bultza/IRIS2-hardware/IRIS2_PCB_CPU/docs/IRIS2_Batteries.png

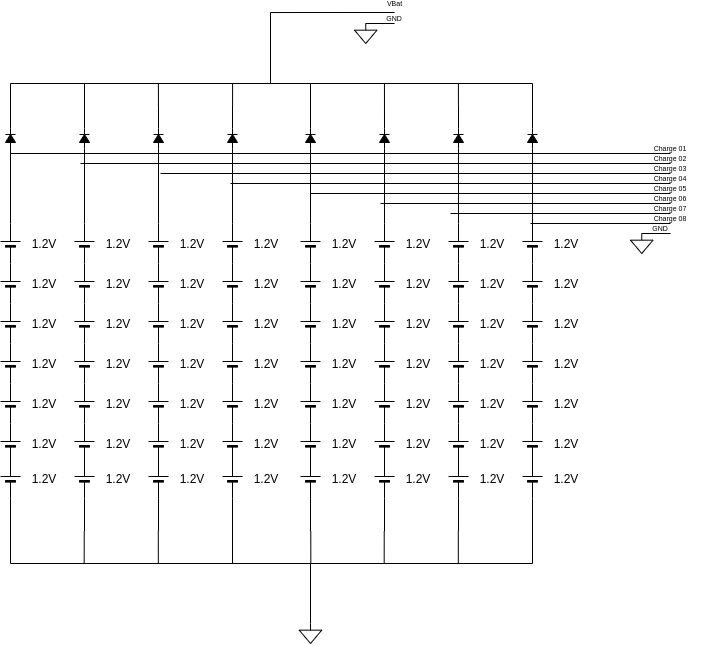
IRIS2_PCB_CPU/docs/IRIS2_Batteries.png
