bultza/IRIS2-hardware/IRIS2_PCB_CPU/Project Outputs for IRIS2_PCB_CPU/3D Render BOTTOM.png

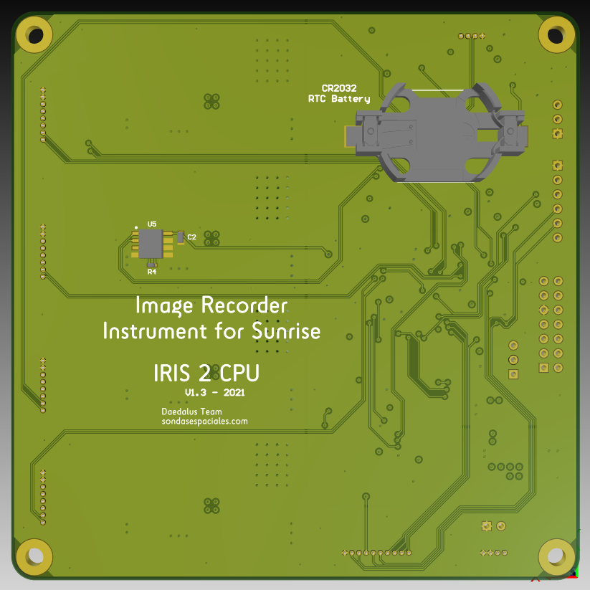
IRIS2_PCB_CPU/Project Outputs for IRIS2_PCB_CPU/3D Render BOTTOM.png
