bultza/IRIS2-hardware/IRIS2_PCB_CPU/Project Outputs for IRIS2_PCB_CPU/3D Render TOP.png

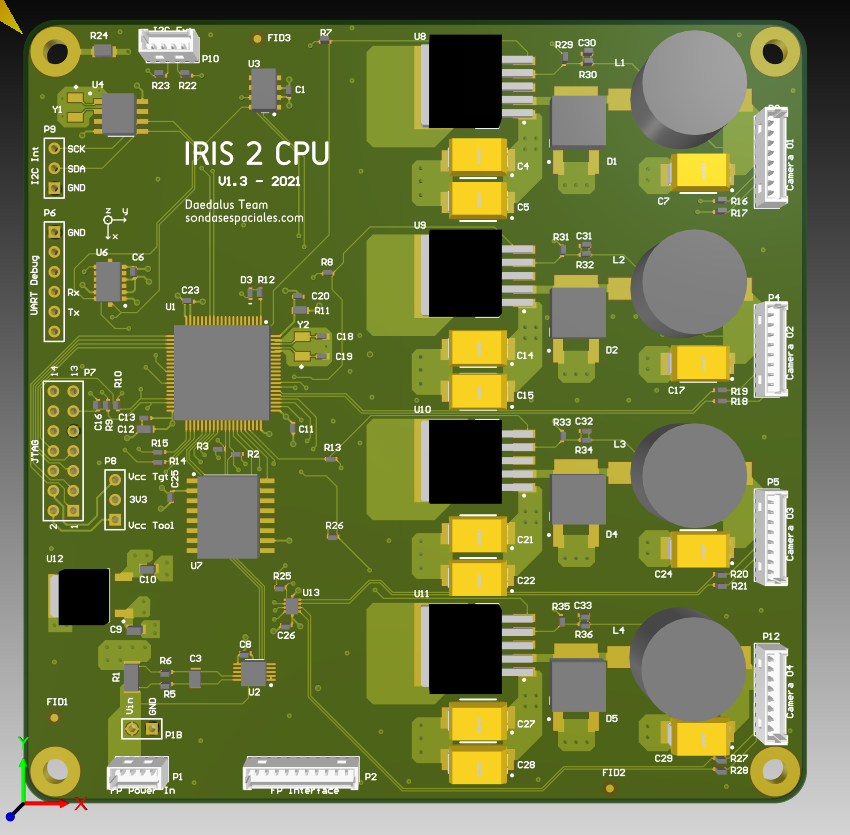
IRIS2_PCB_CPU/Project Outputs for IRIS2_PCB_CPU/3D Render TOP.png
