bultza/IRIS2-hardware/IRIS2_PCB_CPU/Project Outputs for IRIS2_PCB_CPU/20210401_IRIS2_CPU_LayerStack.png

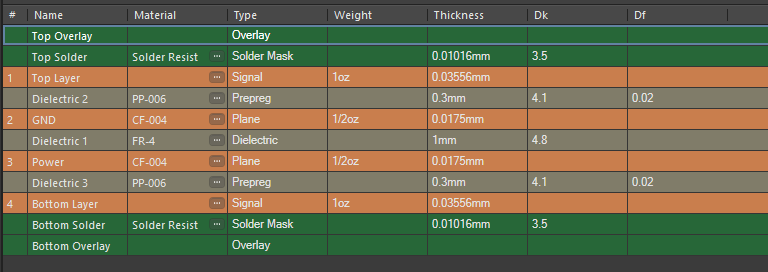
IRIS2_PCB_CPU/Project Outputs for IRIS2_PCB_CPU/20210401_IRIS2_CPU_LayerStack.png
