bultza/IRIS2-hardware/IRIS2_PCB_FrontPlate/docs/datasheets/coockieMonster.webp

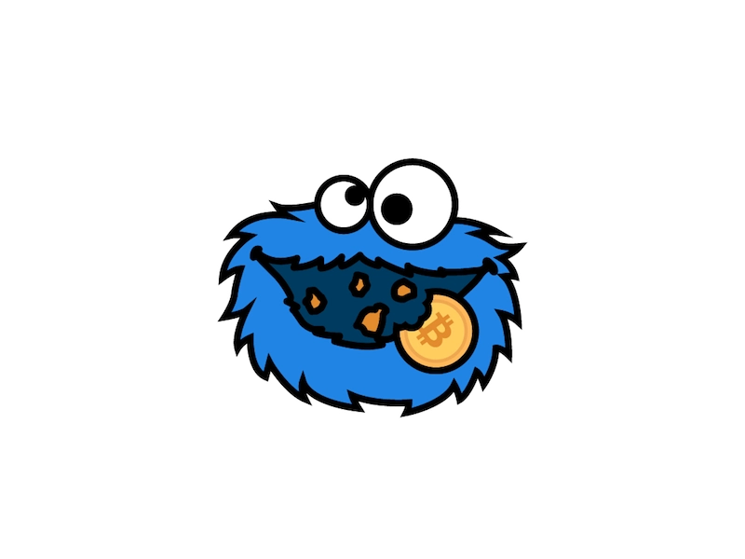
IRIS2_PCB_FrontPlate/docs/datasheets/coockieMonster.webp
